VinceVol/Beatcycle/CAM Work/Beatcycle-Swing_ArmPocket050.dxf

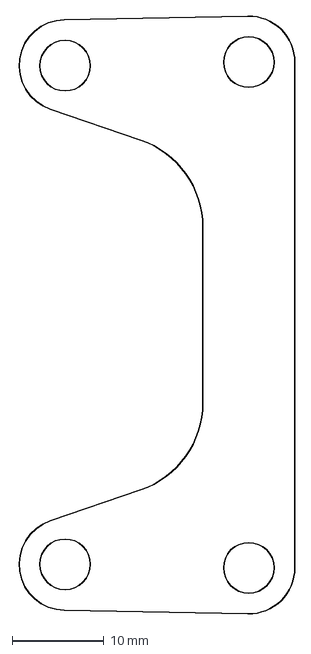
[picture p15: CAD file, 2026-07-15]
CAM Work/Beatcycle-Swing_ArmPocket050.dxf
30.3 x 65.1 mm
