VinceVol/Beatcycle/CAM Work/Step_Files/Beatcycle-Swing_ArmRear_Shock_Rear_Mnt_BrakeSide.step

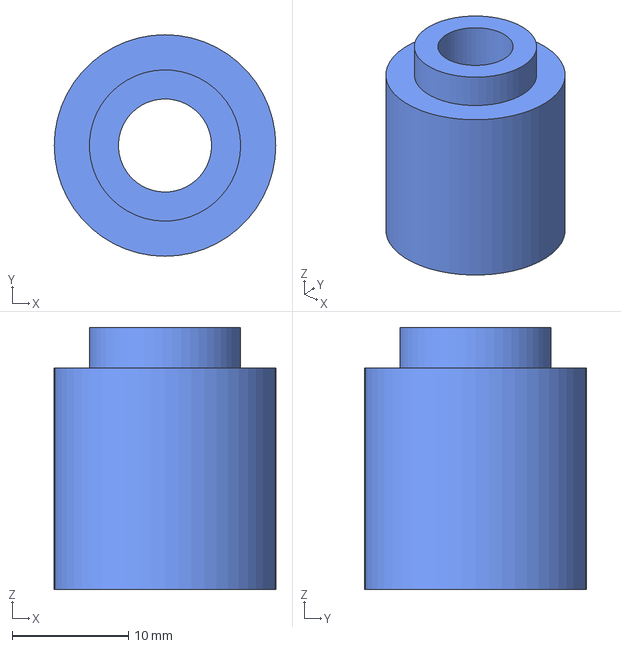
[picture p16: CAD file, 2026-07-15]
CAM Work/Step_Files/Beatcycle-Swing_ArmRear_Shock_Rear_Mnt_BrakeSide.step
19.1 x 19.1 x 22.5 mm
