VinceVol/Beatcycle/Forward_Pivot_pieces.FCStd

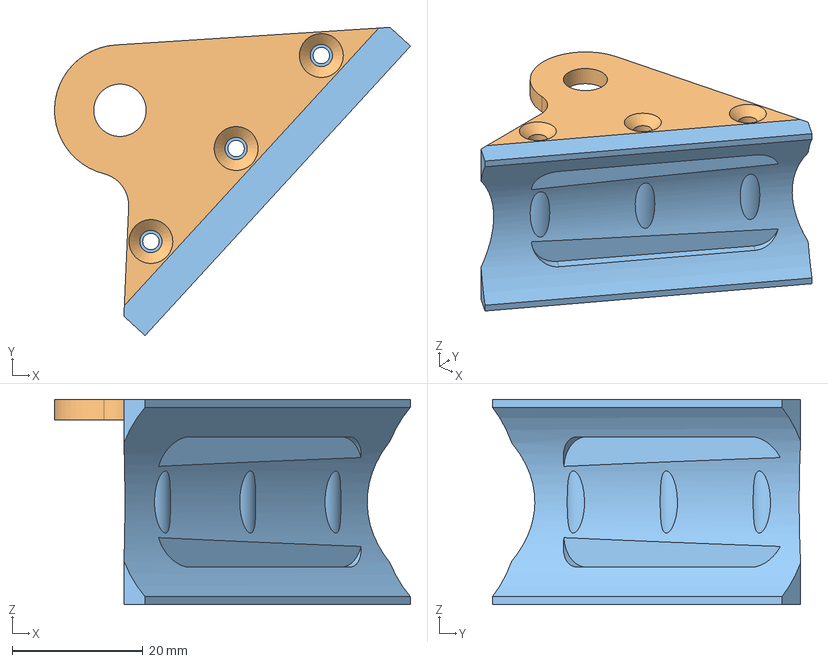
[picture p17: CAD file, 2026-06-27]
Forward_Pivot_pieces.FCStd
54.4 x 47.1 x 31.3 mm
Body (Solid)
