VinceVol/Beatcycle/Jigs/HeadTubeReamJig-BodyPocket001.step

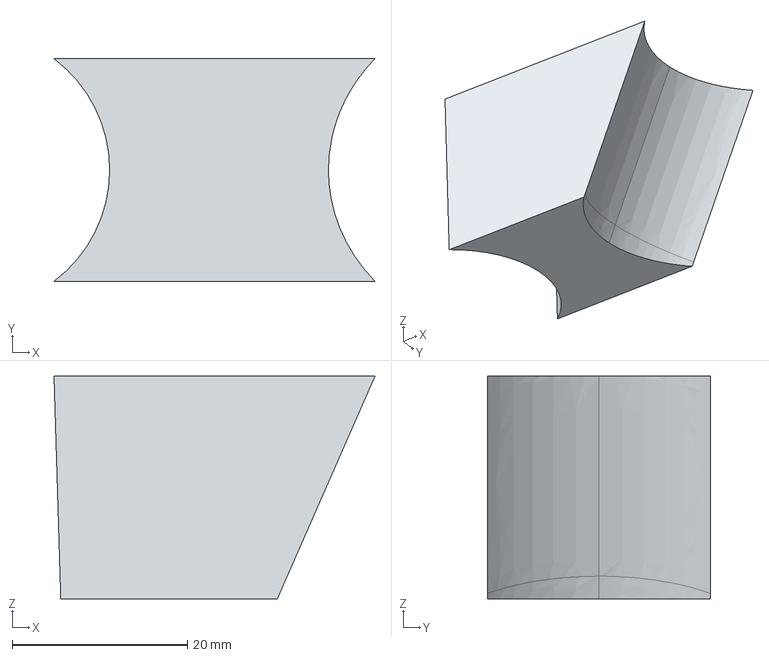
[picture p18: CAD file, 2026-07-15]
Jigs/HeadTubeReamJig-BodyPocket001.step
36.6 x 25.4 x 25.4 mm
