VinceVol/Beatcycle/Simulations/BeatcycleV1.FCStd

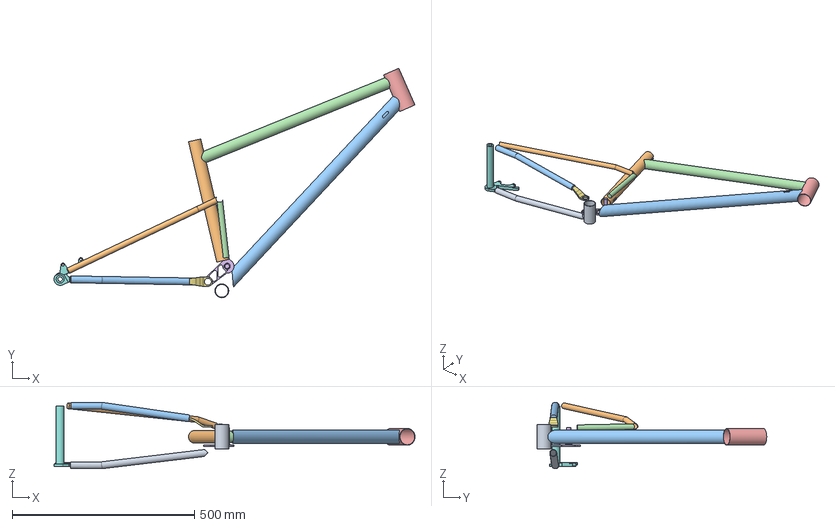
[picture p19: CAD file, 2026-05-06]
Simulations/BeatcycleV1.FCStd
991.4 x 630.3 x 182.4 mm
BB iso 68
SeatTube
DownTube
TopTube
HeadTube
Rear_Shk_Chn_lnk_2
Yoke
UDH_Flat_Mnt_BrakeSide
ChainStay_BrakeSide
SeatStay_DriveSide
ChainStay_DriveSide
MidStay_ChainSide
