VinceVol/Beatcycle/CAM Work/MP_Link_1.FCStd

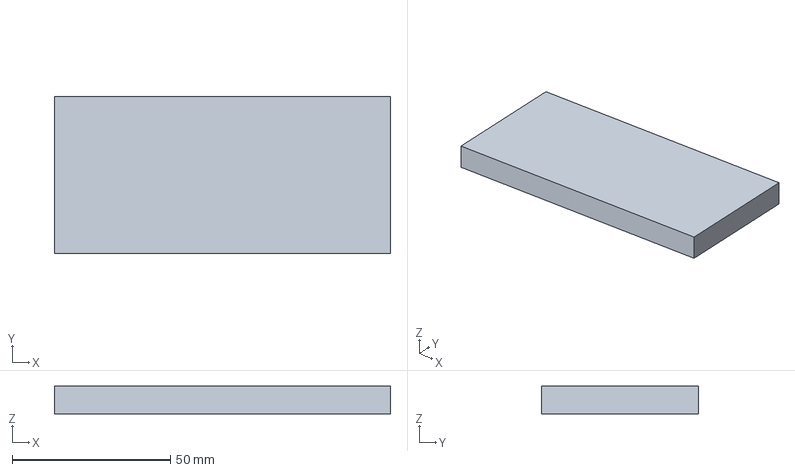
[picture p20: CAD file, 2026-07-15]
CAM Work/MP_Link_1.FCStd
106.2 x 49.5 x 8.80 mm
