VinceVol/Beatcycle/CAM Work/Step_Files/Beatcycle-Swing_ArmYoke.step

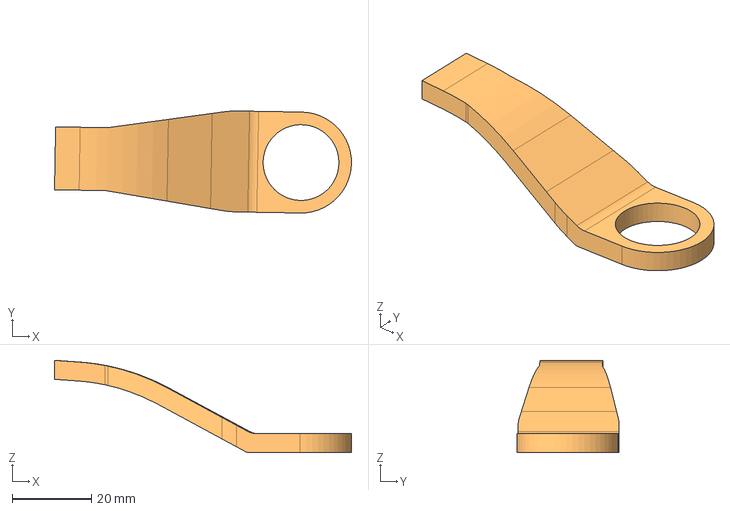
[picture p21: CAD file, 2026-07-15]
CAM Work/Step_Files/Beatcycle-Swing_ArmYoke.step
74.8 x 25.7 x 23.2 mm
