VinceVol/Beatcycle/Forward_Pivot_Sheet_Metal.FCStd

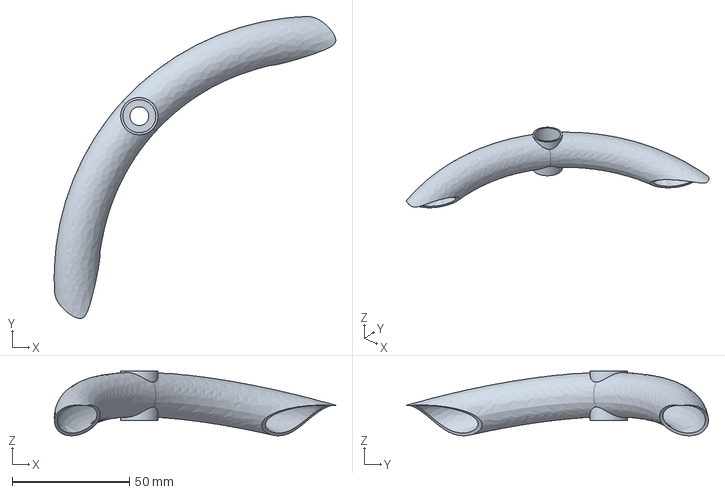
[picture p22: CAD file, 2026-05-27]
Forward_Pivot_Sheet_Metal.FCStd
119.8 x 128.5 x 27.5 mm
