VinceVol/Beatcycle/Jigs/HeadTubeReamJig.FCStd

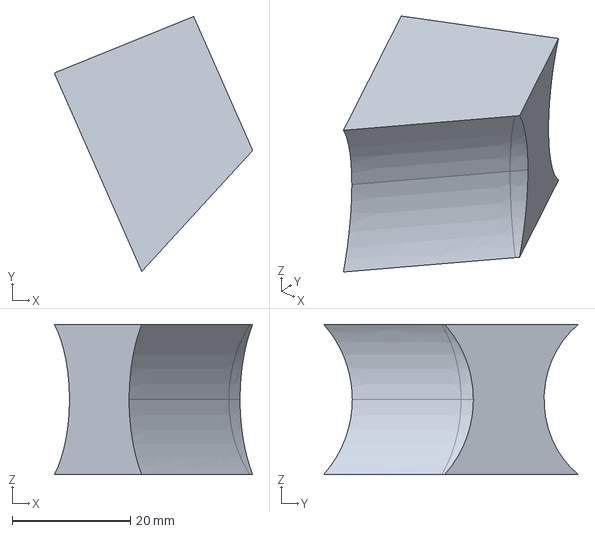
[picture p23: CAD file, 2026-07-15]
Jigs/HeadTubeReamJig.FCStd
33.5 x 43.1 x 25.4 mm
