VinceVol/Beatcycle/Rear_Swing_Arm_Tubing/BrakeSide_Cuts.dxf

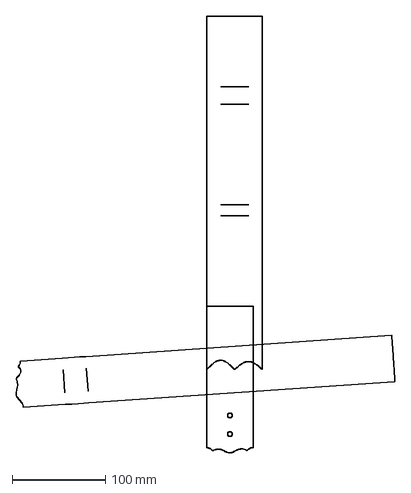
[picture p24: CAD file, 2026-08-04]
Rear_Swing_Arm_Tubing/BrakeSide_Cuts.dxf
406.4 x 468.6 mm
