VinceVol/Beatcycle/CAM Work/V2_FMP_Braze_on.FCStd

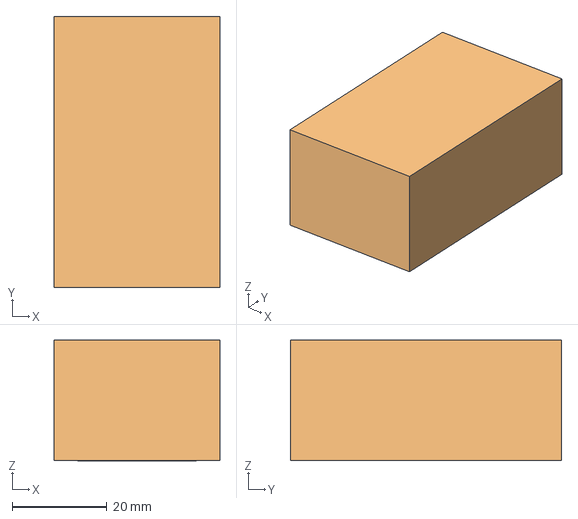
[picture p25: CAD file, 2026-07-15]
CAM Work/V2_FMP_Braze_on.FCStd
35.0 x 57.2 x 25.4 mm
Model-Braze_On_Piece (Solid)003
Stock022
