VinceVol/Beatcycle/Rear_Swing_Arm_Tubing/DriveSide_Swing_Arm_Vert.dxf

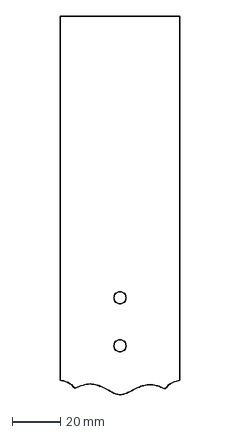
[picture p26: CAD file, 2026-08-04]
Rear_Swing_Arm_Tubing/DriveSide_Swing_Arm_Vert.dxf
49.9 x 157.4 mm
