VinceVol/Beatcycle/CAM Work/SidePiecePad002.dxf

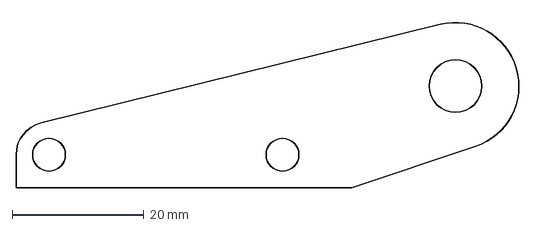
[picture p27: CAD file, 2026-07-15]
CAM Work/SidePiecePad002.dxf
77.5 x 26.1 mm
