VinceVol/Beatcycle/CAM Work/Downtube.dxf

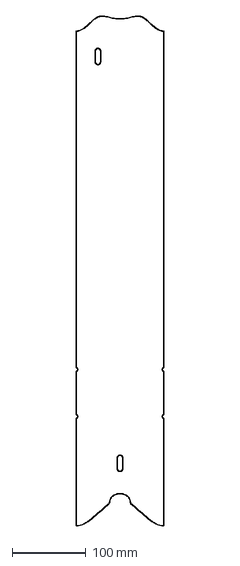
[picture p29: CAD file, 2026-07-15]
CAM Work/Downtube.dxf
119.4 x 689.0 mm
