VinceVol/Beatcycle/Rear_Swing_Arm_Tubing/DriveSide_Cuts.dxf

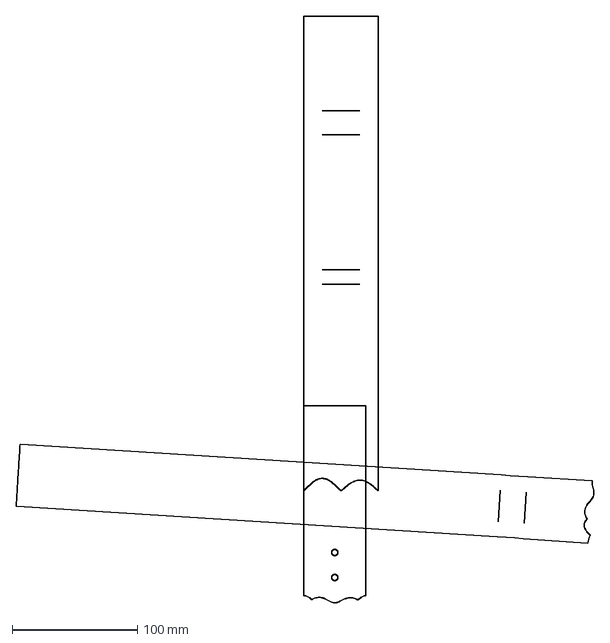
[picture p30: CAD file, 2026-08-04]
Rear_Swing_Arm_Tubing/DriveSide_Cuts.dxf
461.4 x 468.6 mm
