VinceVol/Beatcycle/CAM Work/Yoke.FCStd

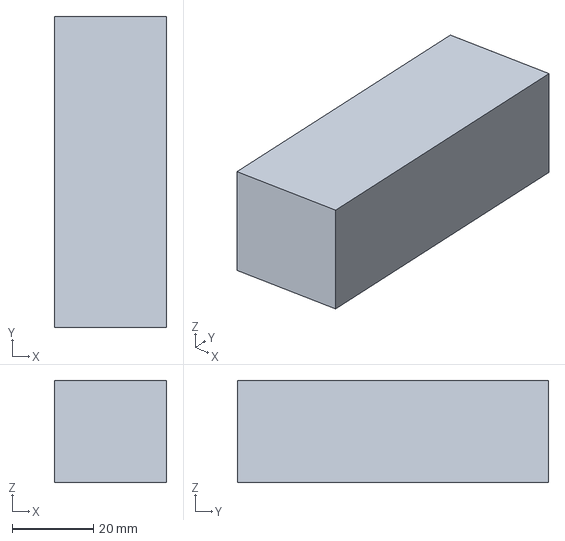
[picture p31: CAD file, 2026-07-15]
CAM Work/Yoke.FCStd
27.7 x 76.7 x 25.2 mm
