VinceVol/Beatcycle/Rear_Swing_Arm_Tubing/ChainStay_DriveSide.FCStd

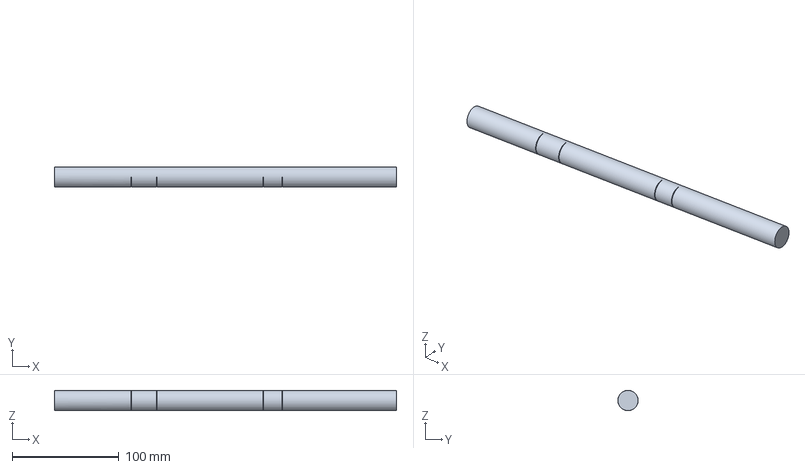
[picture p32: CAD file, 2026-07-16]
Rear_Swing_Arm_Tubing/ChainStay_DriveSide.FCStd
321.1 x 19.1 x 19.1 mm
