VinceVol/Beatcycle/CAM Work/R_SHK_Pivot_Weldon.FCStd

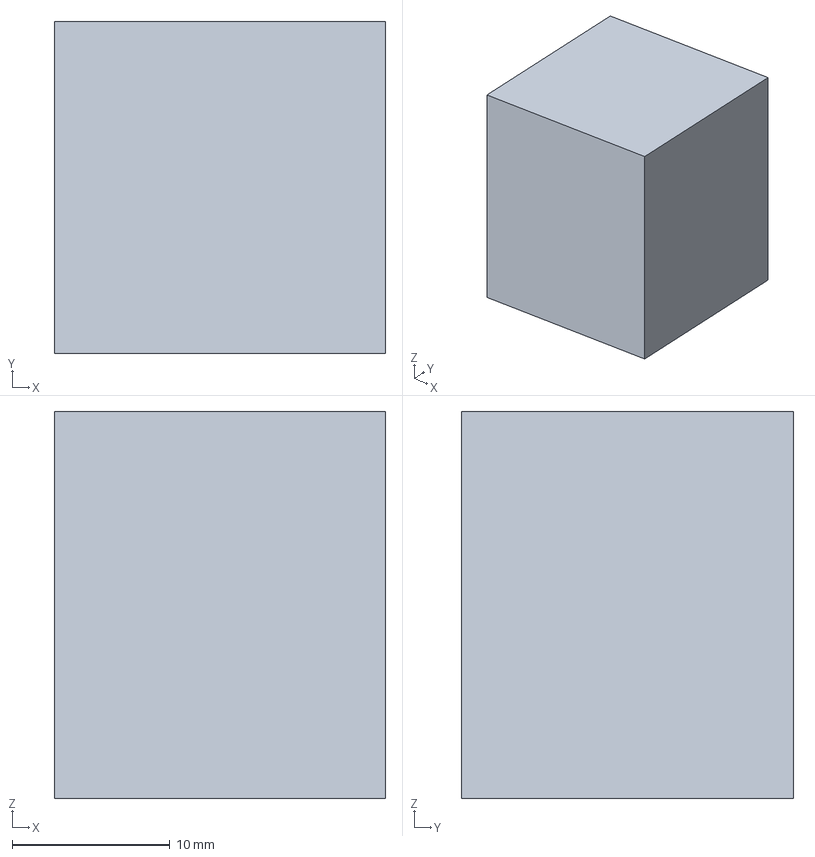
[picture p33: CAD file, 2026-07-15]
CAM Work/R_SHK_Pivot_Weldon.FCStd
21.0 x 21.0 x 24.5 mm
