VinceVol/Beatcycle/Rear_Swing_Arm_Tubing/ChainStay_BrakeSide.FCStd

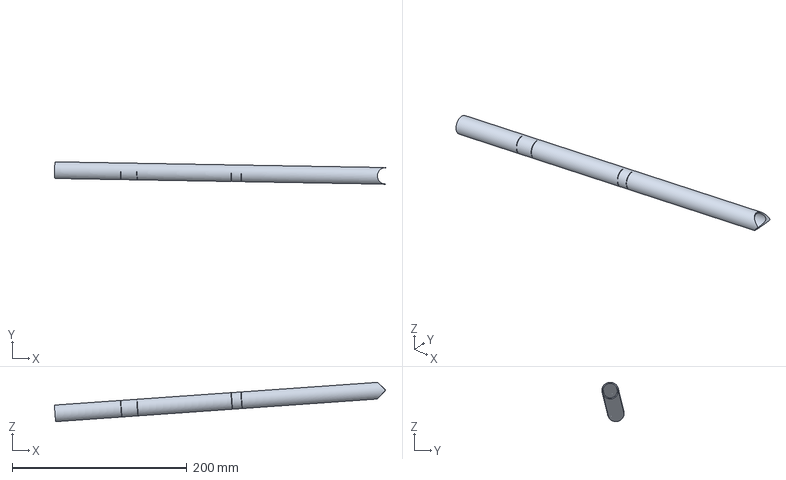
[picture p34: CAD file, 2026-07-15]
Rear_Swing_Arm_Tubing/ChainStay_BrakeSide.FCStd
378.8 x 25.6 x 45.0 mm
