VinceVol/Beatcycle/CAM Work/MP_Link_2.FCStd

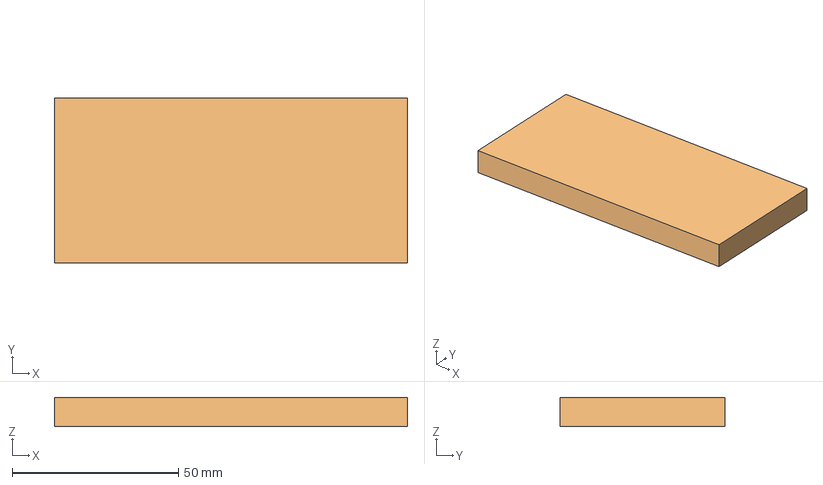
[picture p35: CAD file, 2026-07-15]
CAM Work/MP_Link_2.FCStd
106.2 x 49.6 x 8.80 mm
Model-Body001
Stock005
