VinceVol/Beatcycle/CAM Work/Rear_Shk_Chn_Link_DriveSide.FCStd

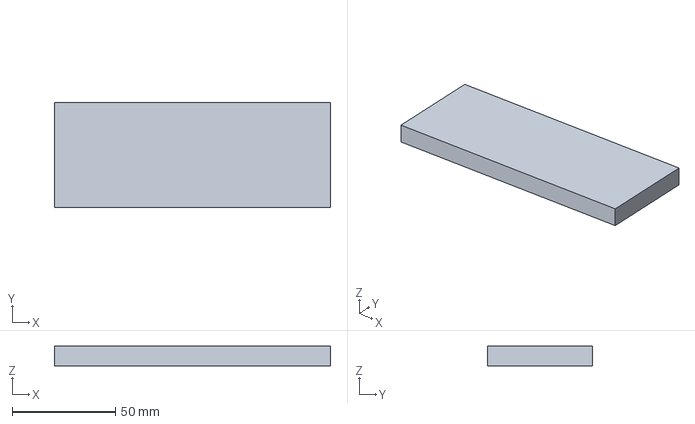
[picture p36: CAD file, 2026-05-26]
CAM Work/Rear_Shk_Chn_Link_DriveSide.FCStd
133.3 x 50.8 x 9.52 mm
