VinceVol/Beatcycle/CAM Work/brake_side_rear_axle.FCStd

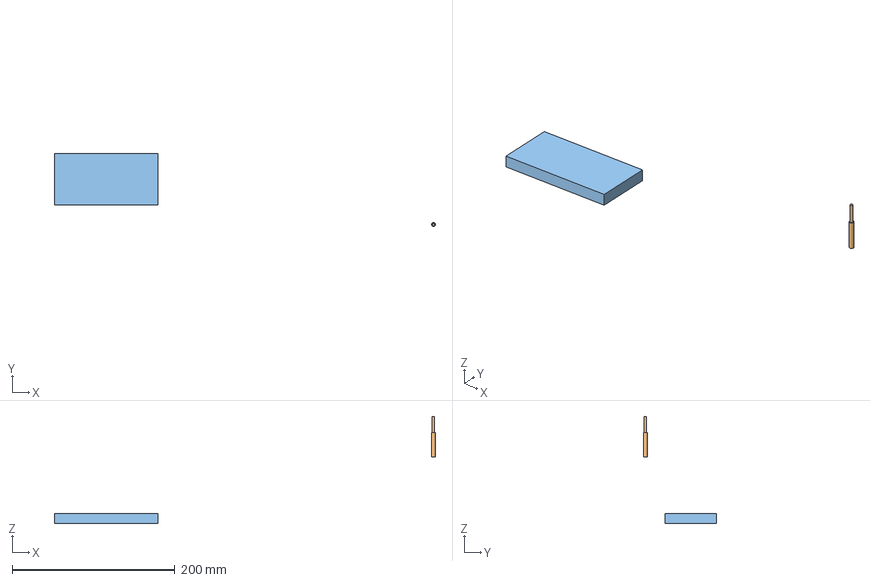
[picture p37: CAD file, 2026-05-26]
CAM Work/brake_side_rear_axle.FCStd
468.4 x 90.1 x 132.0 mm
Model-UDH_Flat_Mnt_BrakeSide (Solid)
Endmill
Stock007
