VinceVol/Beatcycle/CAM Work/drive_side_rear_axle.FCStd

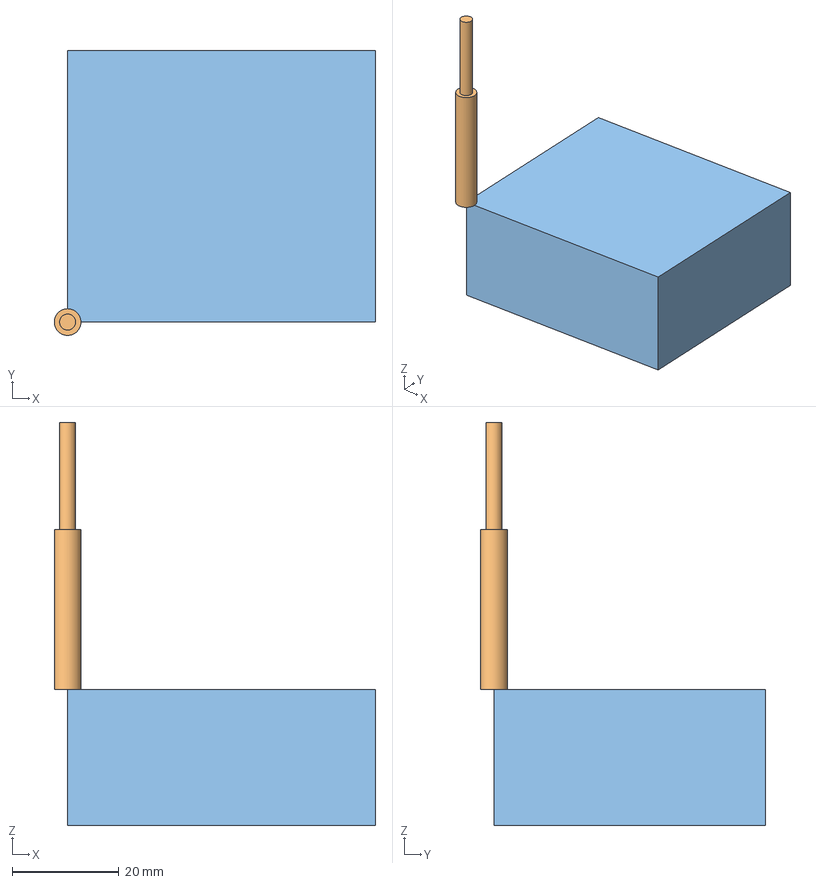
[picture p38: CAD file, 2026-05-26]
CAM Work/drive_side_rear_axle.FCStd
60.1 x 53.3 x 75.4 mm
Model-UDH_DriveSide (Solid)
Endmill
Stock003
